dylanleitenberg-tech/AR_Glasses_Rig/media/carrier_only.png

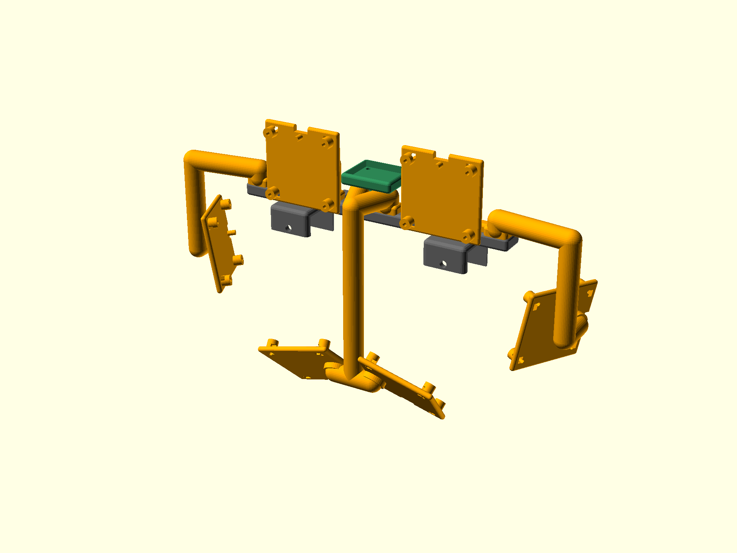
media/carrier_only.png
