dylanleitenberg-tech/AR_Glasses_Rig/media/eye-camera-samples/eyeL_canthus_tracked_1.png

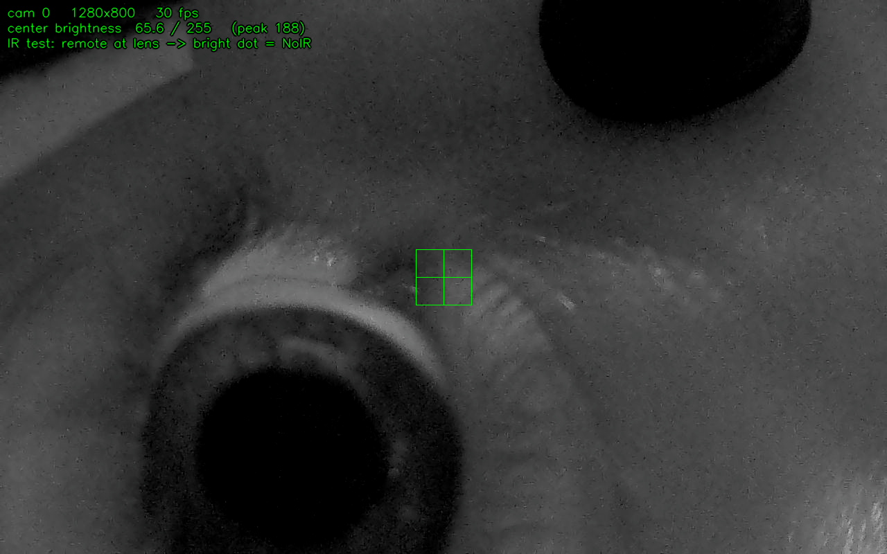
media/eye-camera-samples/eyeL_canthus_tracked_1.png
