dylanleitenberg-tech/AR_Glasses_Rig/media/session-2026-07/led_bracket.png

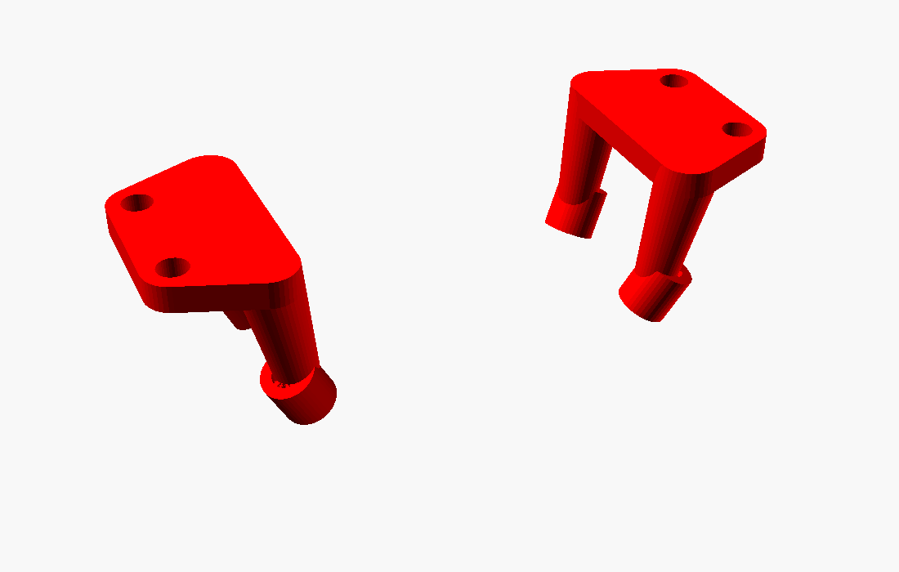
media/session-2026-07/led_bracket.png
