dylanleitenberg-tech/AR_Glasses_Rig/media/session-2026-07/monkey_sprite.png

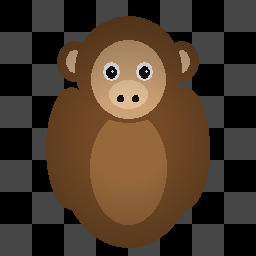
media/session-2026-07/monkey_sprite.png
