dylanleitenberg-tech/AR_Glasses_Rig/media/session-2026-07/overlay_monkeys_demo.png

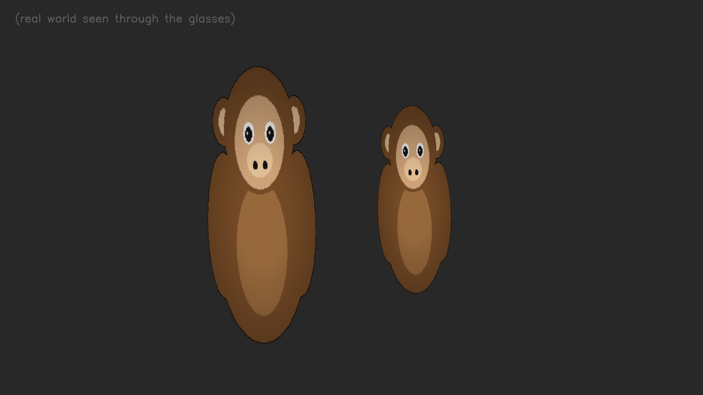
media/session-2026-07/overlay_monkeys_demo.png
