dylanleitenberg-tech/AR_Glasses_Rig/media/session-2026-08-03/eyeL_diag.png

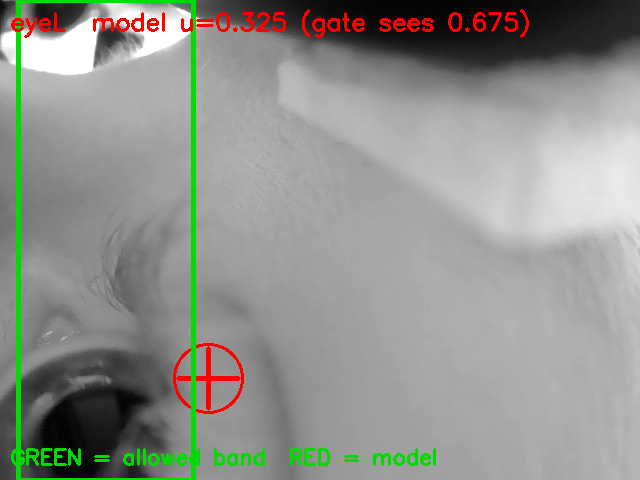
media/session-2026-08-03/eyeL_diag.png
