dylanleitenberg-tech/AR_Glasses_Rig/media/session-2026-08-03/eyeR_ROOM_false_worn.png

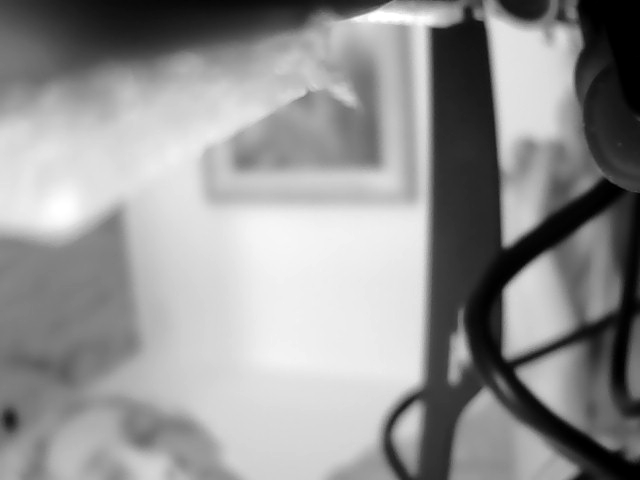
media/session-2026-08-03/eyeR_ROOM_false_worn.png
