dylanleitenberg-tech/AR_Glasses_Rig/media/session-2026-08-03/eyeR_worn_after_adjust.png

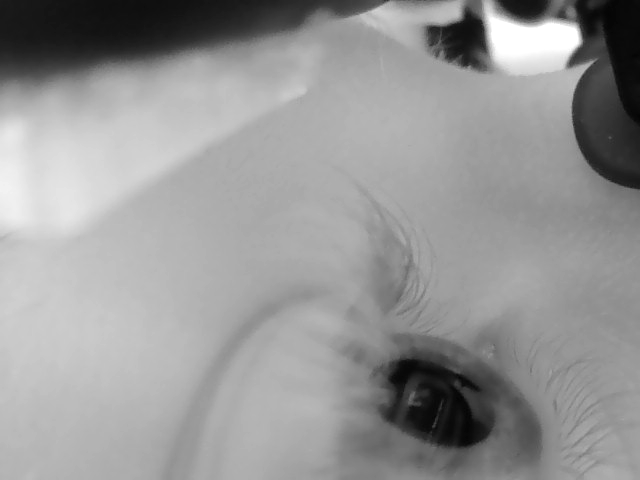
media/session-2026-08-03/eyeR_worn_after_adjust.png
