dylanleitenberg-tech/AR_Glasses_Rig/media/session-2026-08-04/camera_board_bare.jpg

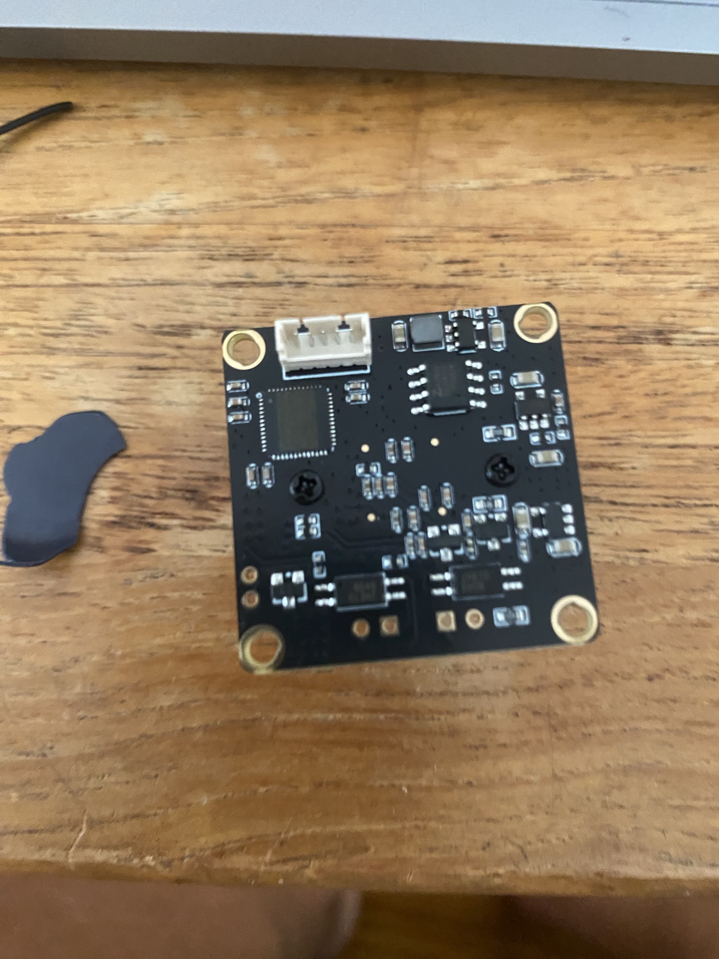
media/session-2026-08-04/camera_board_bare.jpg
