dylanleitenberg-tech/AR_Glasses_Rig/media/session-2026-08-04/sabrent_usb_hub_six_ports.jpg

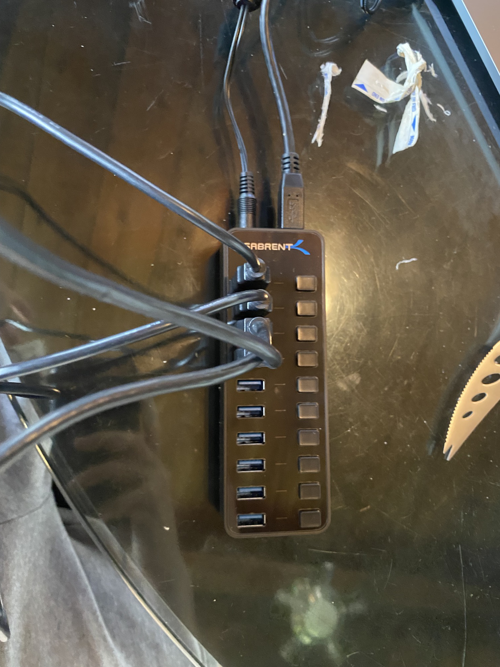
media/session-2026-08-04/sabrent_usb_hub_six_ports.jpg
