dylanleitenberg-tech/AR_Glasses_Rig/media/assembly_front34.png

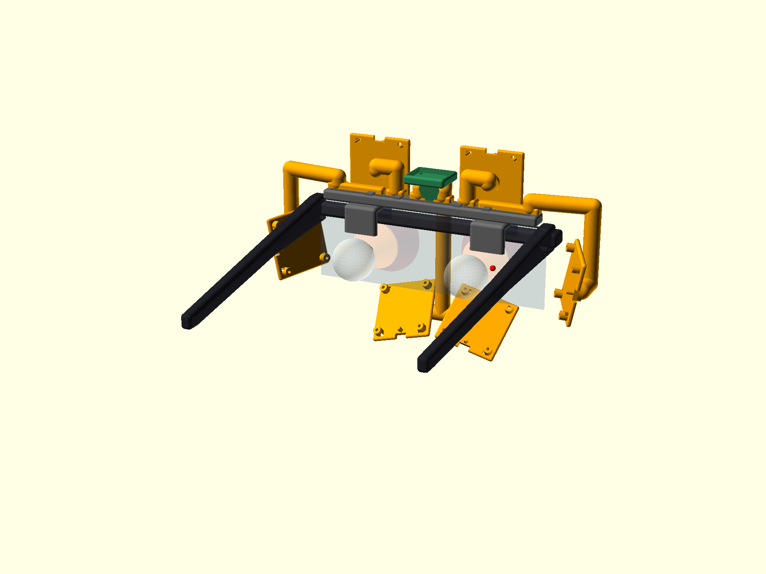
media/assembly_front34.png
