dylanleitenberg-tech/AR_Glasses_Rig/media/assembly_top.png

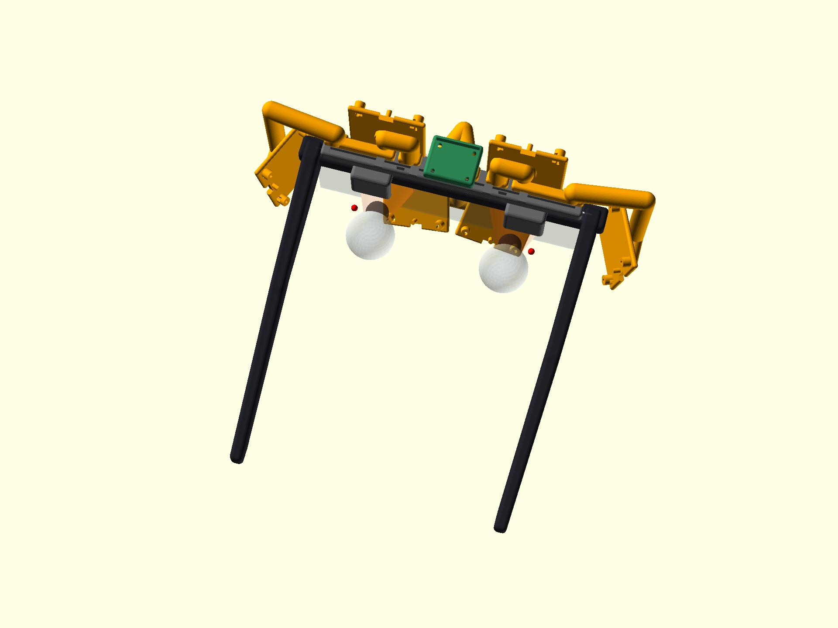
media/assembly_top.png
