dylanleitenberg-tech/AR_Glasses_Rig/media/session-2026-08-04/rig_wired_bench_test.jpg

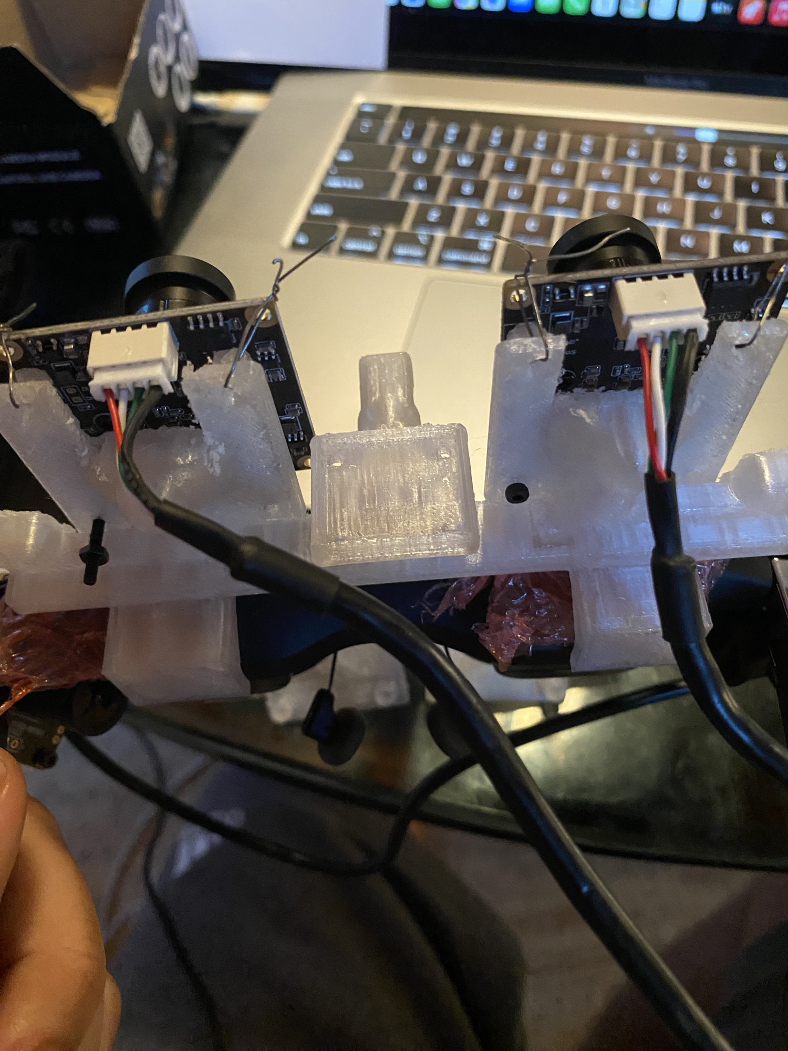
media/session-2026-08-04/rig_wired_bench_test.jpg
