dylanleitenberg-tech/AR_Glasses_Rig/results/kappa_separation.png

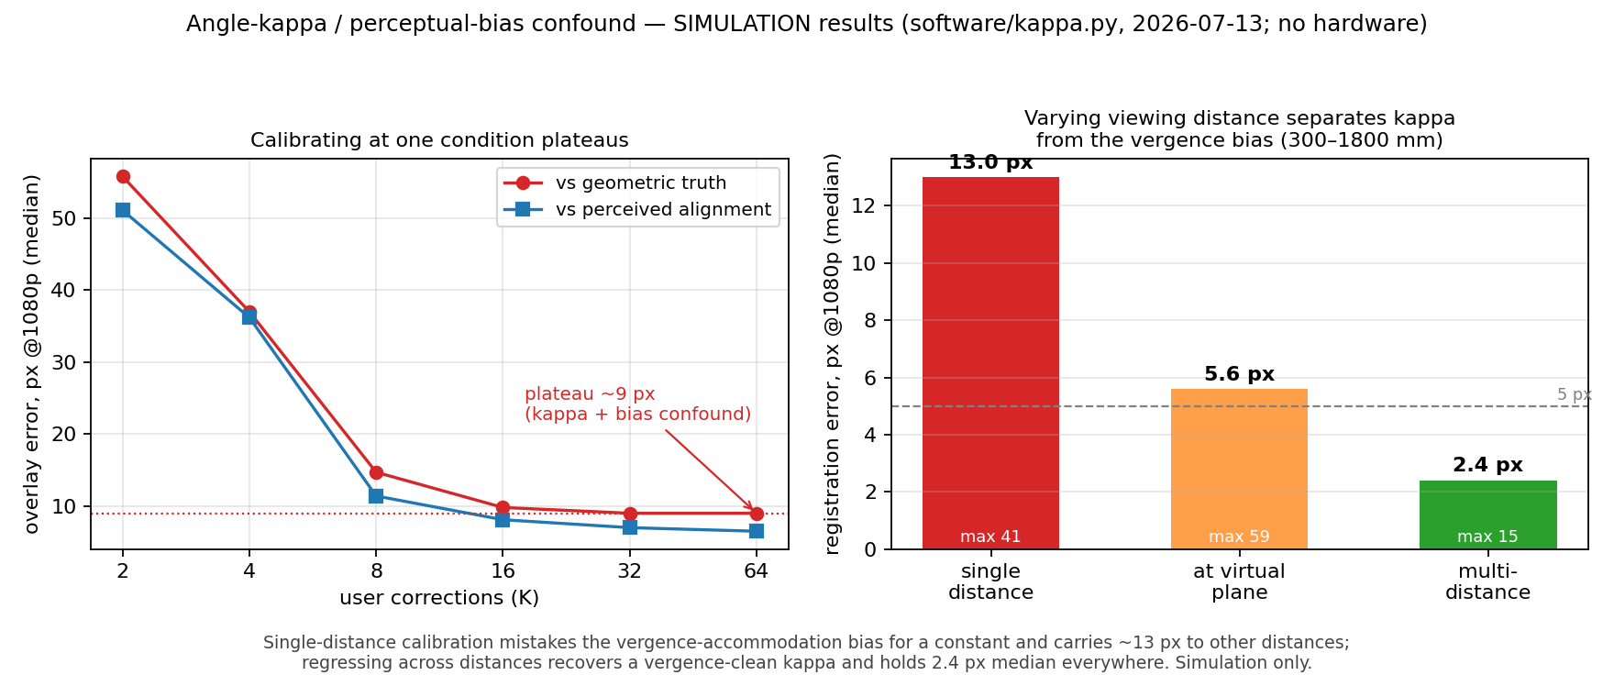
results/kappa_separation.png
