dylanleitenberg-tech/AR_Glasses_Rig/software/content_anchor.py

"""content_anchor.py, PLACE generated content on a real surface and keep it there.

`anchor.py` answers "given a 3D world point, where on the display does it land right now?" It
cannot answer the question that comes first for generated content: *which* 3D point? Today the
only anchors the runtime produces come from `people_track`, content can be stuck to a detected
person and nothing else. There is no way to put an image on a wall, a label on a table, or a
panel in mid-air and have it stay.

This module closes that gap with four pieces:

  1. PLACEMENT   `ray_from_world_cam` turns a world-camera pixel into a world-frame ray, and
                 `raycast_mesh` intersects that ray with the live Delaunay surface from
                 `world_mesh.visible_mesh`. Point the rig at a spot, get the 3D point on the real
                 surface plus its normal. Placement is done in the WORLD-CAMERA frame, not the
                 display frame, so it needs no inverse of the learned calibrator, the mesh and
                 the cameras already share a frame.

  2. ORIENTATION `SurfaceAnchor` holds a position, a surface normal and an up-hint, and emits four
                 world-space corners. The content therefore lies ON the surface and keeps the
                 surface's orientation, it is not a camera-facing billboard like `avatar.py`.
                 Walk around a poster anchored to a wall and it foreshortens correctly.

  3. OCCLUSION   `is_occluded` casts from the camera centre toward the anchor and reports whether
                 real geometry sits in front of it, so content behind a wall can be suppressed
                 rather than painted over it.

  4. PERSISTENCE `AnchorStore` round-trips anchors to JSON so a placement survives the session.

Projection stays with `anchor.AnchorProjector`, the corners are ordinary world points, so they
inherit the parallax-correct, calibrated path already proven there.

Pure numpy + stdlib; `--selftest` runs headless with no cameras and no cv2.

    python3 content_anchor.py --selftest
"""
import argparse
import json
import os
import sys

import numpy as np

from anchor import AnchorProjector, _make_synthetic_device, _rot
from world_mesh import DEFAULT_F, DEFAULT_B
from rig import WORLD_RES

EPS = 1e-9


# --------------------------------------------------------------------------
#  1. Placement: world-camera pixel -> world ray -> surface hit
# --------------------------------------------------------------------------
def ray_from_world_cam(uv, pose, f=DEFAULT_F, res=WORLD_RES):
    """World-camera pixel -> (origin, unit direction) in the WORLD frame.

    `pose` is (R_cw, C) from world_mesh: R_cw maps world->cam, C is the camera centre in world.
    The ray starts at C, so a hit distance is a true metric range from the head.
    """
    R_cw, C = pose
    W = res
    H = int(res * 3 // 4)
    d_cam = np.array([(uv[0] - W / 2.0) / f, (uv[1] - H / 2.0) / f, 1.0])
    d_world = R_cw.T @ d_cam                      # cam->world is the transpose
    n = np.linalg.norm(d_world)
    return np.asarray(C, float).copy(), d_world / (n if n > EPS else 1.0)


def ray_triangle(orig, dirn, v0, v1, v2):
    """Moller-Trumbore. Returns distance along `dirn` to the hit, or None.

    Two-sided on purpose: a surface reconstructed from a point cloud has arbitrary winding, so
    culling by facing would drop half the mesh at random.
    """
    e1 = v1 - v0
    e2 = v2 - v0
    p = np.cross(dirn, e2)
    det = np.dot(e1, p)
    if abs(det) < EPS:
        return None                                # ray parallel to the triangle
    inv = 1.0 / det
    t = orig - v0
    u = np.dot(t, p) * inv
    if u < -EPS or u > 1.0 + EPS:
        return None
    q = np.cross(t, e1)
    v = np.dot(dirn, q) * inv
    if v < -EPS or u + v > 1.0 + EPS:
        return None
    dist = np.dot(e2, q) * inv
    return float(dist) if dist > EPS else None


def raycast_mesh(orig, dirn, verts, faces):
    """Nearest intersection of a ray with the mesh.

    Returns dict(point, normal, distance, face) or None. The normal is flipped to face back
    along the ray so content placed on it always sits on the side you are looking from.
    """
    verts = np.asarray(verts, float)
    faces = np.asarray(faces, int)
    if len(faces) == 0:
        return None
    best = None
    for fi, (a, b, c) in enumerate(faces):
        d = ray_triangle(orig, dirn, verts[a], verts[b], verts[c])
        if d is not None and (best is None or d < best[0]):
            best = (d, fi, a, b, c)
    if best is None:
        return None
    d, fi, a, b, c = best
    n = np.cross(verts[b] - verts[a], verts[c] - verts[a])
    ln = np.linalg.norm(n)
    n = n / ln if ln > EPS else np.array([0.0, 0.0, -1.0])
    if np.dot(n, dirn) > 0:                        # face the viewer
        n = -n
    return {"point": orig + d * dirn, "normal": n, "distance": d, "face": fi}


def fit_plane(points):
    """Least-squares plane through >=3 points -> (centroid, unit normal).

    Used to smooth a local surface patch: a single Delaunay triangle's normal is noisy, so
    content placed on it jitters. Averaging over the neighbourhood is far more stable.
    """
    P = np.asarray(points, float)
    if len(P) < 3:
        raise ValueError("fit_plane needs at least 3 points, got %d" % len(P))
    c = P.mean(0)
    _, _, vt = np.linalg.svd(P - c)
    return c, vt[2] / (np.linalg.norm(vt[2]) or 1.0)   # smallest singular vector = normal
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
